marek-czelen/SmartESC_STM32_v2/tools/vcu_esp32.kicad_sch

## KiCad design tools/vcu_esp32.kicad_sch (2026-07-14)

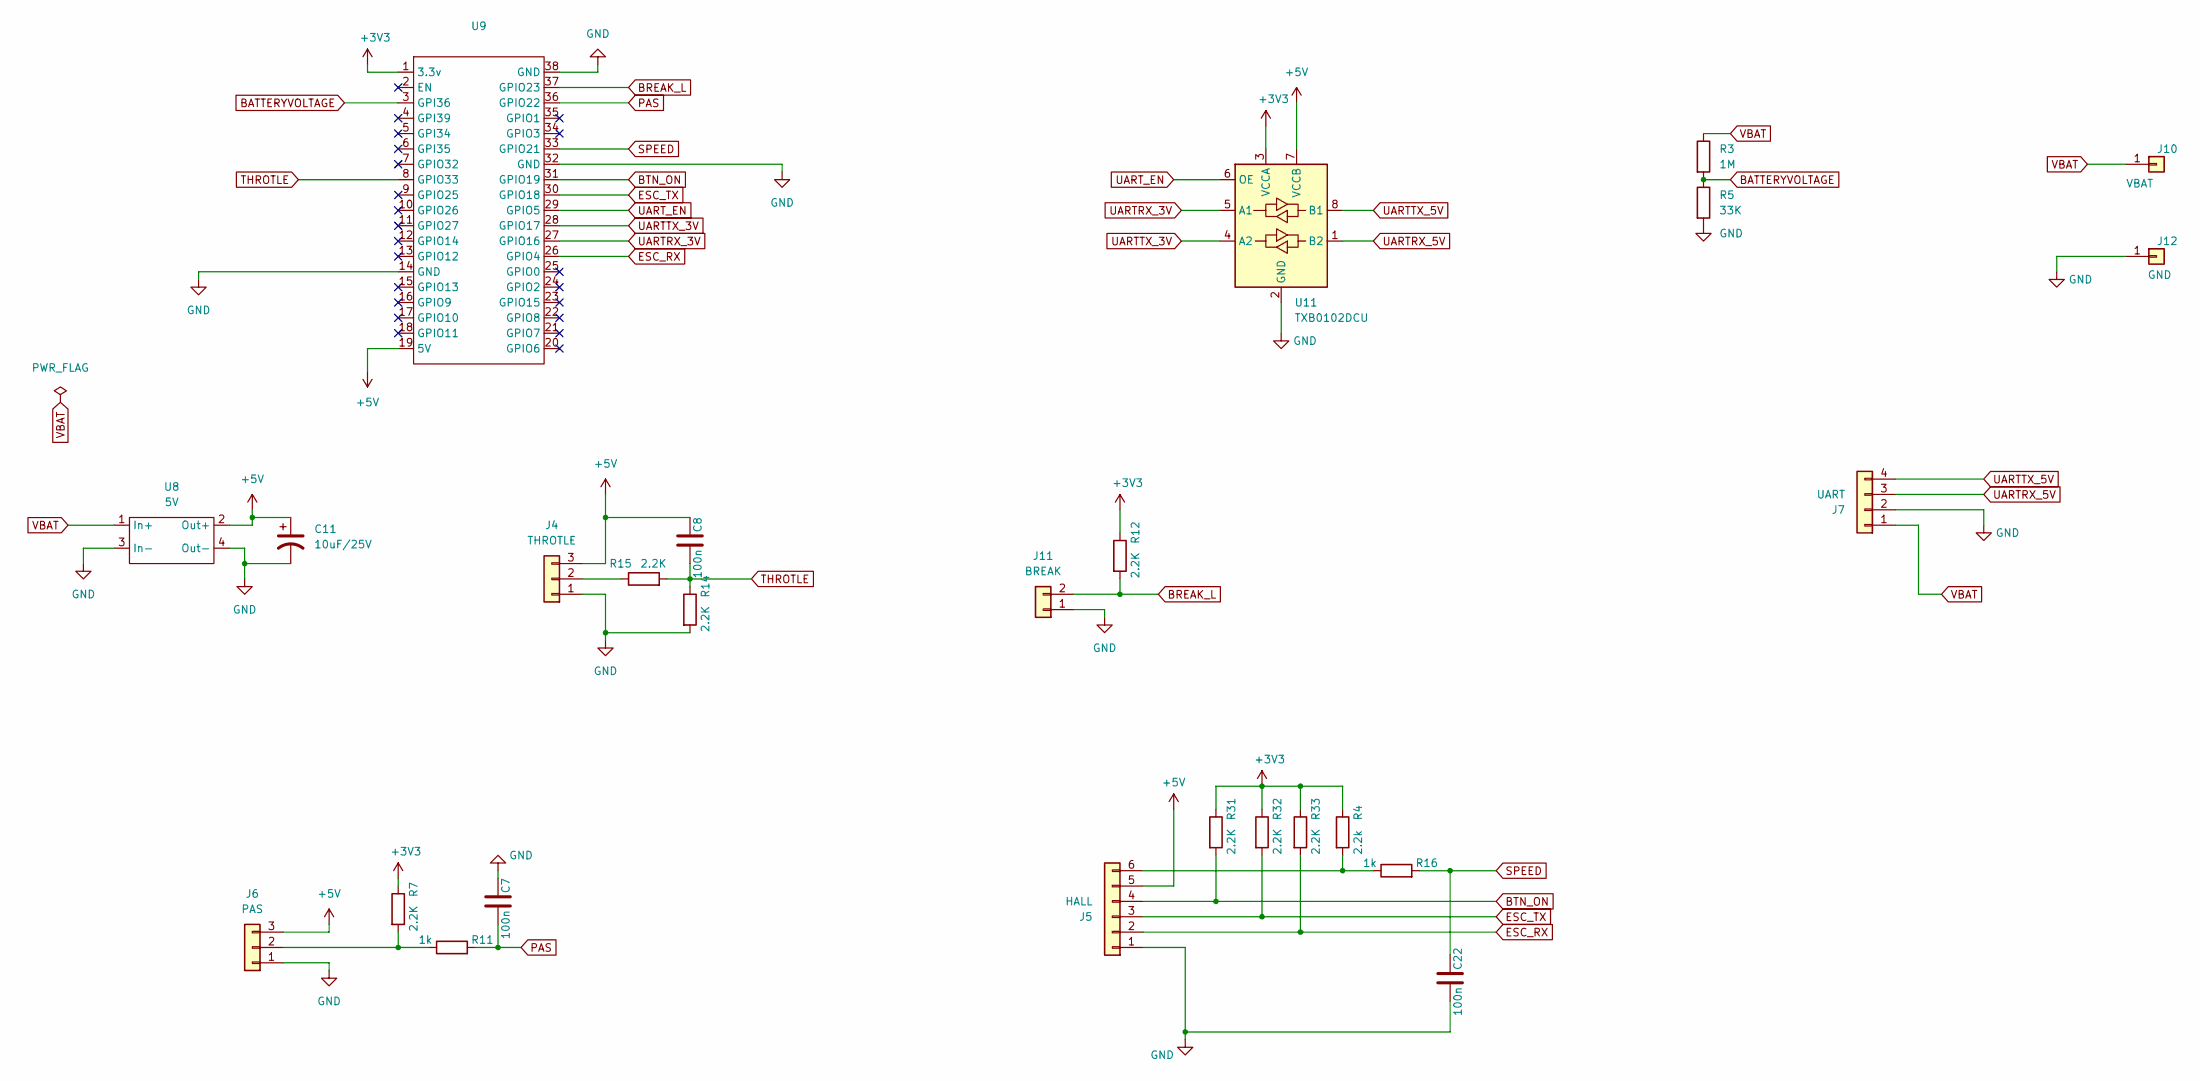
[picture p4: schematic vcu_esp32.kicad_sch]

Parts:
C7, C8, C22: 100n; C_0805_2012Metric
C11: 10uF/25V; CP_Radial_D5.0mm_P2.00mm
J4: THROTLE; PinSocket_1x03_P2.54mm_Vertical
J5: HALL; PinSocket_1x06_P2.54mm_Vertical
J6: PAS; PinSocket_1x03_P2.54mm_Vertical
J7: UART; PinSocket_1x04_P2.54mm_Vertical
J10: VBAT; SolderWire-2.5sqmm_1x01_D2.4mm_OD3.6mm
J11: BREAK; PinSocket_1x02_P2.54mm_Vertical
J12: GND; SolderWire-2.5sqmm_1x01_D2.4mm_OD3.6mm
R3: 1M; R_0805_2012Metric
R4: 2.2k; R_0805_2012Metric
R5: 33K; R_0805_2012Metric
R7, R12, R14, R15, R31, R32, R33: 2.2K; R_0805_2012Metric
R11, R16: 1k; R_0805_2012Metric
U8: 5V; dcdc 5..80V-3.3V
U9: Z_ESP32_DevKitC_38pin_socket
U11: TXB0102DCU; VSSOP-8_2.3x2mm_P0.5mm

Connections:
+3V3: R4.1, R7.1, R12.1, R31.1, R32.1, R33.1, U9.1 (3.3v), U11.3 (VCCA)
+5V: C8.1, C11.1, J4.3, J5.5, J6.3, U8.2 (Out+), U9.19 (5V), U11.7 (VCCB)
BATTERYVOLTAGE: R3.2, R5.1, U9.3 (GPI36)
BREAK_L: J11.2, R12.2, U9.37 (GPIO23)
BTN_ON: J5.4, R31.2, U9.31 (GPIO19)
ESC_RX: J5.2, R33.2, U9.26 (GPIO4)
ESC_TX: J5.3, R32.2, U9.30 (GPIO18)
GND: C7.1, C11.2, C22.2, J4.1, J5.1, J6.1, J7.2, J11.1, J12.1, R5.2, R14.2, U8.3 (In-), U8.4 (Out-), U9.14 (GND), U9.32 (GND), U9.38 (GND), U11.2 (GND)
unnamed: J4.2, R15.1
unnamed: J5.6, R4.2, R16.1
unnamed: J6.2, R7.2, R11.1
PAS: C7.2, R11.2, U9.36 (GPIO22)
SPEED: C22.1, R16.2, U9.33 (GPIO21)
THROTLE: C8.2, R14.1, R15.2, U9.8 (GPIO33)
UARTRX_3V: U9.27 (GPIO16), U11.5 (A1)
UARTRX_5V: J7.3, U11.1 (B2)
UARTTX_3V: U9.28 (GPIO17), U11.4 (A2)
UARTTX_5V: J7.4, U11.8 (B1)
UART_EN: U9.29 (GPIO5), U11.6 (OE)
VBAT: J7.1, J10.1, R3.1, U8.1 (In+)
