marek-czelen/SmartESC_STM32_v2/common_files/MotorControl/MCSDK/MCLib/Any/Inc/enc_align_ctrl.h

/**
  ******************************************************************************
  * @file    enc_align_ctrl.h
  * @author  Motor Control SDK Team, ST Microelectronics
  * @brief   This file contains all definitions and functions prototypes for the
  *          Encoder Alignment Control component of the Motor Control SDK.
  ******************************************************************************
  * @attention
  *
  * <h2><center>&copy; Copyright (c) 2019 STMicroelectronics.
  * All rights reserved.</center></h2>
  *
  * This software component is licensed by ST under Ultimate Liberty license
  * SLA0044, the "License"; You may not use this file except in compliance with
  * the License. You may obtain a copy of the License at:
  *                             www.st.com/SLA0044
  *
  ******************************************************************************
  * @ingroup EncAlignCtrl
  */


/* Define to prevent recursive inclusion -------------------------------------*/
#ifndef __ENCALIGNCTRLCLASS_H
#define __ENCALIGNCTRLCLASS_H

#ifdef __cplusplus
extern "C" {
#endif /* __cplusplus */

/* Includes ------------------------------------------------------------------*/
#include "mc_type.h"
#include "speed_torq_ctrl.h"
#include "virtual_speed_sensor.h"
#include "encoder_speed_pos_fdbk.h"

/** @addtogroup MCSDK
  * @{
  */

/** @addtogroup EncAlignCtrl
  * @{
  */

/**
  * @brief  This structure is used to handle an instance of  EncAlignCtrl component
  */

typedef struct
{
  SpeednTorqCtrl_Handle_t * pSTC;       /*!< Speed and torque controller object used by  EAC.*/
  VirtualSpeedSensor_Handle_t * pVSS;   /*!< Virtual speed sensor object used by EAC.*/
  ENCODER_Handle_t * pENC;              /*!< Encoder object used by EAC.*/
  uint16_t hRemainingTicks;             /*!< Number of clock events remaining to complete
                                             the alignment.*/
  bool EncAligned;   /*!< This flag is true if the encoder has been
                               aligned at least one time, false if hasn't been
                                never aligned.*/
  bool EncRestart;   /*!< This flag is used to force a restart of the
                                motorafter the encoder alignment. It is true
                                if a restart is programmed else false*/
  uint16_t hEACFrequencyHz; /*!< Frequency expressed in Hz at which the user
                                 clocks the EAC calling EAC_Exec method */
  int16_t hFinalTorque;     /*!< Motor torque reference imposed by STC at the
                                 end of programmed alignment. This value
                                 represents actually the Iq current expressed in
                                 digit.*/
  int16_t hElAngle;        /*!< Electrical angle of programmed alignment
                                 expressed in s16degrees.*/
  uint16_t hDurationms;     /*!< Duration of the programmed alignment expressed
                                 in milliseconds.*/
  uint8_t bElToMecRatio;    /*!< Coefficient used to transform electrical to
                                 mechanical quantities and viceversa. It usually
                                 coincides with motor pole pairs number*/
} EncAlign_Handle_t;


/* Exported functions ------------------------------------------------------- */

/*  Function used to initialize an instance of the EncAlignCtrl component */
void EAC_Init( EncAlign_Handle_t * pHandle, SpeednTorqCtrl_Handle_t * pSTC, VirtualSpeedSensor_Handle_t * pVSS,
               ENCODER_Handle_t * pENC );

/* Function used to start the encoder alignment procedure.*/
void EAC_StartAlignment( EncAlign_Handle_t * pHandle );

/* Function used to clocks the encoder alignment controller*/
bool EAC_Exec( EncAlign_Handle_t * pHandle );

/* It returns true if the encoder has been aligned at least one time*/
bool EAC_IsAligned( EncAlign_Handle_t * pHandle );

/* It sets a restart after an encoder alignment*/
void EAC_SetRestartState( EncAlign_Handle_t * pHandle, bool restart );

/* Returns true if a restart after an encoder alignment has been requested*/
bool EAC_GetRestartState( EncAlign_Handle_t * pHandle );

/**
  * @}
  */

/**
  * @}
  */
#ifdef __cplusplus
}
#endif /* __cpluplus */

#endif /* __ENCALIGNCTRLCLASS_H */

/******************* (C) COPYRIGHT 2019 STMicroelectronics *****END OF FILE****/
