marek-czelen/SmartESC_STM32_v2/common_files/MotorControl/MCSDK/MCLib/Any/Inc/pqd_motor_power_measurement.h

/**
  ******************************************************************************
  * @file    pqd_motor_power_measurement.h
  * @author  Motor Control SDK Team, ST Microelectronics
  * @brief   This file contains all definitions and functions prototypes for the
  *          pqd_motor_power_measurement component of the Motor Control SDK.
  ******************************************************************************
  * @attention
  *
  * <h2><center>&copy; Copyright (c) 2019 STMicroelectronics.
  * All rights reserved.</center></h2>
  *
  * This software component is licensed by ST under Ultimate Liberty license
  * SLA0044, the "License"; You may not use this file except in compliance with
  * the License. You may obtain a copy of the License at:
  *                             www.st.com/SLA0044
  *
  ******************************************************************************
  * @ingroup motorpowermeasurement
  */

/* Define to prevent recursive inclusion -------------------------------------*/
#ifndef __PQD_MOTORPOWERMEASUREMENT_H
#define __PQD_MOTORPOWERMEASUREMENT_H

#ifdef __cplusplus
extern "C" {
#endif /* __cplusplus */

/* Includes ------------------------------------------------------------------*/
#include "motor_power_measurement.h"
#include "bus_voltage_sensor.h"


/** @addtogroup MCSDK
  * @{
  */

/** @addtogroup motorpowermeasurement
  * @{
  */

/** @addtogroup pqd_motorpowermeasurement
  * @{
  */

typedef struct
{
  MotorPowMeas_Handle_t _super;

  int32_t wConvFact; /* It is the conversion factor used to convert the
                         variables expressed in digit into variables expressed
                         in physical measurement unit. It is used to convert the
                         power in watts. It must be equal to
                         (1000 * 3 * Vddï¿½)/(sqrt(3) * Rshunt * Aop) */

  pFOCVars_t pFOCVars;    /*!< Pointer to FOC vars used by MPM.*/
  BusVoltageSensor_Handle_t * pVBS;              /*!< Bus voltage sensor object used by MPM.*/
  uint16_t meas_count;
} PQD_MotorPowMeas_Handle_t;



/**
  * @brief Implementation of derived class init method. It should be called before each motor restart.
  * @param pHandle related component instance.
  * @retval none.
  */
void PQD_Clear( PQD_MotorPowMeas_Handle_t * pHandle );

/**
  * @brief Implementation of derived class CalcElMotorPower.
  * @param pHandle related component instance.
  * @retval int16_t The measured motor power expressed in watt.
  */
void PQD_CalcElMotorPower( PQD_MotorPowMeas_Handle_t * pHandle );


/**
  * @}
  */

/**
  * @}
  */

/** @} */
#ifdef __cplusplus
}
#endif /* __cpluplus */

#endif /* __CCC_H */

/************************ (C) COPYRIGHT 2019 STMicroelectronics *****END OF FILE****/
