marek-czelen/SmartESC_STM32_v2/common_files/MotorControl/MCSDK/MCLib/Any/Src/r_divider_bus_voltage_sensor.c

/**
  ******************************************************************************
  * @file    r_divider_bus_voltage_sensor.c
  * @author  Motor Control SDK Team, ST Microelectronics
  * @brief   This file provides firmware functions that implement the  features
  *          of the Resistor Divider Bus Voltage Sensor component of the Motor
  *          Control SDK:
  *
  ******************************************************************************
  * @attention
  *
  * <h2><center>&copy; Copyright (c) 2019 STMicroelectronics.
  * All rights reserved.</center></h2>
  *
  * This software component is licensed by ST under Ultimate Liberty license
  * SLA0044, the "License"; You may not use this file except in compliance with
  * the License. You may obtain a copy of the License at:
  *                             www.st.com/SLA0044
  *
  ******************************************************************************
  */

/* Includes ------------------------------------------------------------------*/
#include "r_divider_bus_voltage_sensor.h"
#include "regular_conversion_manager.h"


/** @addtogroup MCSDK
  * @{
  */

/** @addtogroup BusVoltageSensor
  * @{
  */

/** @defgroup RDividerBusVoltageSensor Resistor Divider Bus Voltage Sensor
  * @brief Resistor Divider Bus Voltage Sensor implementation
  *
  * @todo Document the Resistor Divider Bus Voltage Sensor "module".
  *
  * @{
  */

/**
  * @brief  It initializes bus voltage conversion (ADC, ADC channel, conversion time. 
    It must be called only after PWMC_Init.
  * @param  pHandle related RDivider_Handle_t
  * @retval none
  */
__weak void RVBS_Init( RDivider_Handle_t * pHandle )
{
  /* Need to be register with RegularConvManager */
  pHandle->convHandle = RCM_RegisterRegConv(&pHandle->VbusRegConv);
  /* Check */
  RVBS_Clear( pHandle );
}


/**
  * @brief  It clears bus voltage FW variable containing average bus voltage
  *         value
  * @param  pHandle related RDivider_Handle_t
  * @retval none
  */
__weak void RVBS_Clear( RDivider_Handle_t * pHandle )
{
  uint16_t aux;
  uint16_t index;

  aux = ( pHandle->OverVoltageThreshold + pHandle->UnderVoltageThreshold ) / 2u;
  for ( index = 0u; index < pHandle->LowPassFilterBW; index++ )
  {
    pHandle->aBuffer[index] = aux;
  }
  pHandle->_Super.LatestConv = aux;
  pHandle->_Super.AvBusVoltage_d = aux;
  pHandle->index = 0;
}

static uint16_t RVBS_ConvertVbusFiltrered( RDivider_Handle_t * pHandle )
{
  uint16_t hAux;
  uint8_t vindex;
  uint16_t max = 0, min = 0;
  uint32_t tot = 0u;

  for ( vindex = 0; vindex < pHandle->LowPassFilterBW; )
  {
    hAux = RCM_ExecRegularConv(pHandle->convHandle);

    if ( hAux != 0xFFFFu )
    {
      if ( vindex == 0 )
      {
        min = hAux;
        max = hAux;
      }
      else
      {
        if ( hAux < min )
        {
          min = hAux;
        }
        if ( hAux > max )
        {
          max = hAux;
        }
      }
      vindex++;

      tot += hAux;
    }
  }

  tot -= max;
  tot -= min;
  return ( uint16_t )( tot / ( pHandle->LowPassFilterBW - 2u ) );
}

/**
  * @brief  It actually performes the Vbus ADC conversion and updates average
  *         value
  * @param  pHandle related RDivider_Handle_t
  * @retval uint16_t Fault code error
  */
__weak uint16_t RVBS_CalcAvVbusFilt( RDivider_Handle_t * pHandle )
{
  uint32_t wtemp;
  uint16_t hAux;
  uint8_t i;

  hAux = RVBS_ConvertVbusFiltrered( pHandle );

  if ( hAux != 0xFFFF )
  {
    pHandle->aBuffer[pHandle->index] = hAux;
    wtemp = 0;
    for ( i = 0; i < pHandle->LowPassFilterBW; i++ )
    {
      wtemp += pHandle->aBuffer[i];
    }
    wtemp /= pHandle->LowPassFilterBW;
    pHandle->_Super.AvBusVoltage_d = ( uint16_t )wtemp;
    pHandle->_Super.LatestConv = hAux;

    if ( pHandle->index < pHandle->LowPassFilterBW - 1 )
    {
      pHandle->index++;
    }
    else
    {
      pHandle->index = 0;
    }
  }

  pHandle->_Super.FaultState = RVBS_CheckFaultState( pHandle );

  return ( pHandle->_Super.FaultState );
}

/**
  * @brief  It actually performes the Vbus ADC conversion and updates average
  *         value
  * @param  pHandle related RDivider_Handle_t
  * @retval uint16_t Fault code error
  */
__weak uint16_t RVBS_CalcAvVbus( RDivider_Handle_t * pHandle )
{
  uint32_t wtemp;
  uint16_t hAux;
  uint8_t i;

  hAux = RCM_ExecRegularConv(pHandle->convHandle);

  if ( hAux != 0xFFFF )
  {
    pHandle->aBuffer[pHandle->index] = hAux;
    wtemp = 0;
    for ( i = 0; i < pHandle->LowPassFilterBW; i++ )
    {
      wtemp += pHandle->aBuffer[i];
    }
    wtemp /= pHandle->LowPassFilterBW;
    pHandle->_Super.AvBusVoltage_d = ( uint16_t )wtemp;
    pHandle->_Super.LatestConv = hAux;

    if ( pHandle->index < pHandle->LowPassFilterBW - 1 )
    {
      pHandle->index++;
    }
    else
    {
      pHandle->index = 0;
    }
  }

  pHandle->_Super.FaultState = RVBS_CheckFaultState( pHandle );

  return ( pHandle->_Super.FaultState );
}

/**
  * @brief  It returns MC_OVER_VOLT, MC_UNDER_VOLT or MC_NO_ERROR depending on
  *         bus voltage and protection threshold values
  * @param  pHandle related RDivider_Handle_t
  * @retval uint16_t Fault code error
  */
__weak uint16_t RVBS_CheckFaultState( RDivider_Handle_t * pHandle )
{
  uint16_t fault;

  if ( (pHandle->OverVoltageThreshold > 0) && (pHandle->_Super.AvBusVoltage_d > pHandle->OverVoltageThreshold))
  {
		fault = MC_OVER_VOLT;
  }
  else if ( (pHandle->UnderVoltageThreshold > 0) && (pHandle->_Super.AvBusVoltage_d < pHandle->UnderVoltageThreshold))
  {

    fault = MC_UNDER_VOLT;
  }
  else
  {
    fault = MC_NO_ERROR;
  }
  return fault;
}


/**
  * @}
  */

/**
  * @}
  */

/** @} */

/************************ (C) COPYRIGHT 2019 STMicroelectronics *****END OF FILE****/
