marek-czelen/SmartESC_STM32_v2/common_files/inc/mcconf_default.h

/*
	Copyright 2016 - 2019 Benjamin Vedder	benjamin@vedder.se

	This file is part of the VESC firmware.

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
    You should have received a copy of the GNU General Public License
    along with this program.  If not, see <http://www.gnu.org/licenses/>.
    */

#ifndef MCCONF_DEFAULT_H_
#define MCCONF_DEFAULT_H_

// Default settings
#ifndef MCCONF_DEFAULT_MOTOR_TYPE
#define MCCONF_DEFAULT_MOTOR_TYPE		MOTOR_TYPE_FOC
#endif
#ifndef MCCONF_PWM_MODE
#define MCCONF_PWM_MODE					PWM_MODE_SYNCHRONOUS // Default PWM mode
#endif
#ifndef MCCONF_SENSOR_MODE
#define MCCONF_SENSOR_MODE				SENSOR_MODE_SENSORED // Sensor mode
#endif
#ifndef MCCONF_COMM_MODE
#define MCCONF_COMM_MODE				COMM_MODE_INTEGRATE	// The commutation mode to use
#endif

// Limits
#ifndef MCCONF_L_CURRENT_MAX
#define MCCONF_L_CURRENT_MAX			30.0	// Current limit in Amperes (Upper)
#endif
#ifndef MCCONF_L_CURRENT_MIN
#define MCCONF_L_CURRENT_MIN			-30.0	// Current limit in Amperes (Lower)
#endif
#ifndef MCCONF_L_IN_CURRENT_MAX
#define MCCONF_L_IN_CURRENT_MAX			20.0	// Input current limit in Amperes (Upper)
#endif
#ifndef MCCONF_L_IN_CURRENT_MIN
#define MCCONF_L_IN_CURRENT_MIN			-20.0	// Input current limit in Amperes (Lower)
#endif
#ifndef MCCONF_L_MAX_ABS_CURRENT
#define MCCONF_L_MAX_ABS_CURRENT		60.0	// The maximum absolute current above which a fault is generated
#endif
#ifndef MCCONF_L_MIN_VOLTAGE
#define MCCONF_L_MIN_VOLTAGE			8.0		// Minimum input voltage
#endif
#ifndef MCCONF_L_MAX_VOLTAGE
#define MCCONF_L_MAX_VOLTAGE			56.0	// Maximum input voltage
#endif
#ifndef MCCONF_L_BATTERY_CUT_START
#define MCCONF_L_BATTERY_CUT_START		34.0	// Start limiting the positive current at this voltage
#endif
#ifndef MCCONF_L_BATTERY_CUT_END
#define MCCONF_L_BATTERY_CUT_END		30.0		// Limit the positive current completely at this voltage
#endif
#ifndef MCCONF_L_RPM_MAX
#define MCCONF_L_RPM_MAX				60000.0	// The motor speed limit (Upper)
#endif
#ifndef MCCONF_L_RPM_MIN
#define MCCONF_L_RPM_MIN				-60000.0	// The motor speed limit (Lower)
#endif
#ifndef MCCONF_L_RPM_START
#define MCCONF_L_RPM_START				1.0		// Fraction of full speed where RPM current limiting starts
#endif
#ifndef MCCONF_L_SLOW_ABS_OVERCURRENT
#define MCCONF_L_SLOW_ABS_OVERCURRENT	true	// Use the filtered (and hence slower) current for the overcurrent fault detection
#endif
#ifndef MCCONF_L_MIN_DUTY
#define MCCONF_L_MIN_DUTY				0.00	// Minimum duty cycle
#endif
#ifndef MCCONF_L_MAX_DUTY
#define MCCONF_L_MAX_DUTY				0.99	// Maximum duty cycle
#endif
#ifndef MCCONF_L_CURR_MAX_RPM_FBRAKE
#define MCCONF_L_CURR_MAX_RPM_FBRAKE	300		// Maximum electrical RPM to use full brake at
#endif
#ifndef MCCONF_L_CURR_MAX_RPM_FBRAKE_CC
#define MCCONF_L_CURR_MAX_RPM_FBRAKE_CC	1500	// Maximum electrical RPM to use full brake at with current control
#endif
#ifndef MCCONF_L_LIM_TEMP_FET_START
#define MCCONF_L_LIM_TEMP_FET_START		65.0	// MOSFET temperature where current limiting should begin
#endif
#ifndef MCCONF_L_LIM_TEMP_FET_END
#define MCCONF_L_LIM_TEMP_FET_END		75.0	// MOSFET temperature where everything should be shut off
#endif
#ifndef MCCONF_L_LIM_TEMP_MOTOR_START
#define MCCONF_L_LIM_TEMP_MOTOR_START	0.0	// MOTOR temperature where current limiting should begin
#endif
#ifndef MCCONF_L_LIM_TEMP_MOTOR_END
#define MCCONF_L_LIM_TEMP_MOTOR_END		75.0	// MOTOR temperature where everything should be shut off
#endif
#ifndef MCCONF_L_LIM_TEMP_ACCEL_DEC
#define MCCONF_L_LIM_TEMP_ACCEL_DEC		0.15	// Decrease temperature limits this much during acceleration
#endif
#ifndef MCCONF_L_WATT_MAX
#define MCCONF_L_WATT_MAX				1500000.0	// Maximum wattage output
#endif
#ifndef MCCONF_L_WATT_MIN
#define MCCONF_L_WATT_MIN				-1500000.0	// Minimum wattage output (braking)
#endif
#ifndef MCCONF_L_CURRENT_MAX_SCALE
#define MCCONF_L_CURRENT_MAX_SCALE		1.0	// Maximum current scale
#endif
#ifndef MCCONF_L_CURRENT_MIN_SCALE
#define MCCONF_L_CURRENT_MIN_SCALE		1.0	// Minimum current scale
#endif
#ifndef MCCONF_L_DUTY_START
#define MCCONF_L_DUTY_START				1.0 // Start limiting current at this duty cycle
#endif

// Speed PID parameters
#ifndef MCCONF_S_PID_KP
#define MCCONF_S_PID_KP					2	// Proportional gain
#endif
#ifndef MCCONF_S_PID_KI
#define MCCONF_S_PID_KI					5	// Integral gain
#endif
#ifndef MCCONF_S_PID_KD
#define MCCONF_S_PID_KD					0.0	// Derivative gain
#endif
#ifndef MCCONF_S_PID_KD_FILTER
#define MCCONF_S_PID_KD_FILTER			0.2	// Derivative filter
#endif
#ifndef MCCONF_S_PID_MIN_RPM
#define MCCONF_S_PID_MIN_RPM			0.0	// Minimum allowed RPM
#endif
#ifndef MCCONF_S_PID_ALLOW_BRAKING
#define MCCONF_S_PID_ALLOW_BRAKING		false	// Allow braking in speed control mode
#endif
#ifndef MCCONF_S_PID_RAMP_ERPMS_S
#define MCCONF_S_PID_RAMP_ERPMS_S		0.0	// Default Speed Input Ramp
#endif

// Position PID parameters
#ifndef MCCONF_P_PID_KP
#define MCCONF_P_PID_KP					0.03	// Proportional gain
#endif
#ifndef MCCONF_P_PID_KI
#define MCCONF_P_PID_KI					0.0		// Integral gain
#endif
#ifndef MCCONF_P_PID_KD
#define MCCONF_P_PID_KD					0.0004	// Derivative gain
#endif
#ifndef MCCONF_P_PID_KD_FILTER
#define MCCONF_P_PID_KD_FILTER			0.2		// Derivative filter
#endif
#ifndef MCCONF_P_PID_ANG_DIV
#define MCCONF_P_PID_ANG_DIV			1.0		// Divide angle by this value
#endif

// Current control parameters
#ifndef MCCONF_CC_GAIN
#define MCCONF_CC_GAIN					0.0046	// Current controller error gain
#endif
#ifndef MCCONF_CC_MIN_CURRENT
#define MCCONF_CC_MIN_CURRENT			0.05	// Minimum allowed current
#endif
#ifndef MCCONF_CC_STARTUP_BOOST_DUTY
#define MCCONF_CC_STARTUP_BOOST_DUTY	0.01	// The lowest duty cycle to use in current control mode (has to be > MCPWM_MIN_DUTY_CYCLE)
#endif
#ifndef MCCONF_CC_RAMP_STEP
#define MCCONF_CC_RAMP_STEP				0.04	// Maximum duty cycle ramping step in CC mode
#endif

// BLDC
#ifndef MCCONF_SL_MIN_RPM
#define MCCONF_SL_MIN_RPM				150		// Auto-commutate below this RPM
#endif
#ifndef MCCONF_SL_MIN_ERPM_CYCLE_INT_LIMIT
#define MCCONF_SL_MIN_ERPM_CYCLE_INT_LIMIT	1100.0	// Minimum RPM to calculate the BEMF coupling from
#endif
#ifndef MCCONF_SL_CYCLE_INT_LIMIT
#define MCCONF_SL_CYCLE_INT_LIMIT		62.0	// Flux integrator limit 0 ERPM
#endif
#ifndef MCCONF_SL_BEMF_COUPLING_K
#define MCCONF_SL_BEMF_COUPLING_K		600.0	// Input voltage to bemf coupling constant
#endif
#ifndef MCCONF_SL_PHASE_ADVANCE_AT_BR
#define MCCONF_SL_PHASE_ADVANCE_AT_BR	0.8		// Flux integrator limit percentage at MCPWM_CYCLE_INT_START_RPM_BR ERPM
#endif
#ifndef MCCONF_SL_CYCLE_INT_BR
#define MCCONF_SL_CYCLE_INT_BR			80000.0	// RPM border between the START and LOW interval
#endif
#ifndef MCCONF_SL_MAX_FB_CURR_DIR_CHANGE
#define MCCONF_SL_MAX_FB_CURR_DIR_CHANGE	10.0	// Maximum current during full brake during which a direction change is allowed
#endif

// BLDC hall sensor table
#ifndef MCCONF_HALL_TAB_0
#define MCCONF_HALL_TAB_0				-1
#endif
#ifndef MCCONF_HALL_TAB_1
#define MCCONF_HALL_TAB_1				1
#endif
#ifndef MCCONF_HALL_TAB_2
#define MCCONF_HALL_TAB_2				3
#endif
#ifndef MCCONF_HALL_TAB_3
#define MCCONF_HALL_TAB_3				2
#endif
#ifndef MCCONF_HALL_TAB_4
#define MCCONF_HALL_TAB_4				5
#endif
#ifndef MCCONF_HALL_TAB_5
#define MCCONF_HALL_TAB_5				6
#endif
#ifndef MCCONF_HALL_TAB_6
#define MCCONF_HALL_TAB_6				4
#endif
#ifndef MCCONF_HALL_TAB_7
#define MCCONF_HALL_TAB_7				-1
#endif
#ifndef MCCONF_HALL_ERPM
#define MCCONF_HALL_ERPM				2000.0	// ERPM above which sensorless commutation is used in hybrid mode
#endif

// FOC
#ifndef MCCONF_FOC_CURRENT_KP
#define MCCONF_FOC_CURRENT_KP			0.09
#endif
#ifndef MCCONF_FOC_CURRENT_KI
#define MCCONF_FOC_CURRENT_KI			110.0
#endif
#ifndef MCCONF_FOC_F_SW
#define MCCONF_FOC_F_SW					16000.0
#endif
#ifndef MCCONF_FOC_DT_US
#define MCCONF_FOC_DT_US				0.12 // Microseconds for dead time compensation
#endif
#ifndef MCCONF_FOC_ENCODER_INVERTED
#define MCCONF_FOC_ENCODER_INVERTED		false
#endif
#ifndef MCCONF_FOC_ENCODER_OFFSET
#define MCCONF_FOC_ENCODER_OFFSET		90.0
#endif
#ifndef MCCONF_FOC_ENCODER_RATIO
#define MCCONF_FOC_ENCODER_RATIO		7.0
#endif
#ifndef MCCONF_FOC_SENSOR_MODE
#define MCCONF_FOC_SENSOR_MODE			FOC_SENSOR_MODE_SENSORLESS
#endif
#ifndef MCCONF_FOC_PLL_KP
#define MCCONF_FOC_PLL_KP				2000.0
#endif
#ifndef MCCONF_FOC_PLL_KI
#define MCCONF_FOC_PLL_KI				30000.0
#endif
#ifndef MCCONF_FOC_MOTOR_L
#define MCCONF_FOC_MOTOR_L				0.0001
#endif
#ifndef MCCONF_FOC_MOTOR_R
#define MCCONF_FOC_MOTOR_R				0.1
#endif
#ifndef MCCONF_FOC_MOTOR_FLUX_LINKAGE
#define MCCONF_FOC_MOTOR_FLUX_LINKAGE	0.012
#endif
#ifndef MCCONF_FOC_MOTOR_LD_LQ_DIFF
#define MCCONF_FOC_MOTOR_LD_LQ_DIFF		0.0
#endif
#ifndef MCCONF_FOC_OBSERVER_GAIN
#define MCCONF_FOC_OBSERVER_GAIN		9e7		// Can be something like 600 / L
#endif
#ifndef MCCONF_FOC_OBSERVER_GAIN_SLOW
#define MCCONF_FOC_OBSERVER_GAIN_SLOW	0.05	// Observer gain scale at minimum duty cycle
#endif
#ifndef MCCONF_FOC_DUTY_DOWNRAMP_KP
#define MCCONF_FOC_DUTY_DOWNRAMP_KP		10.0	// PI controller for duty control when decreasing the duty
#endif
#ifndef MCCONF_FOC_DUTY_DOWNRAMP_KI
#define MCCONF_FOC_DUTY_DOWNRAMP_KI		200.0	// PI controller for duty control when decreasing the duty
#endif
#ifndef MCCONF_FOC_OPENLOOP_RPM
#define MCCONF_FOC_OPENLOOP_RPM			1500.0	// Openloop RPM (sensorless low speed or when finding index pulse)
#endif
#ifndef MCCONF_FOC_OPENLOOP_RPM_LOW
#define MCCONF_FOC_OPENLOOP_RPM_LOW		0.0		// Fraction of OPENLOOP_RPM at minimum motor current
#endif
#ifndef MCCONF_FOC_D_GAIN_SCALE_START
#define MCCONF_FOC_D_GAIN_SCALE_START	0.9		// Start reducing D axis current controller gain at this modulation
#endif
#ifndef MCCONF_FOC_D_GAIN_SCALE_MAX_MOD
#define MCCONF_FOC_D_GAIN_SCALE_MAX_MOD	0.2		// D axis currnet controller gain at maximum modulation
#endif
#ifndef MCCONF_FOC_SL_OPENLOOP_HYST
#define MCCONF_FOC_SL_OPENLOOP_HYST		0.1		// Time below min RPM to activate openloop (s)
#endif
#ifndef MCCONF_FOC_SL_OPENLOOP_TIME
#define MCCONF_FOC_SL_OPENLOOP_TIME		0.05	// Time to remain in openloop after ramping (s)
#endif
#ifndef MCCONF_FOC_SL_OPENLOOP_T_LOCK
#define MCCONF_FOC_SL_OPENLOOP_T_LOCK	0.0		// Time to lock motor in beginning of open loop sequence
#endif
#ifndef MCCONF_FOC_SL_OPENLOOP_T_RAMP
#define MCCONF_FOC_SL_OPENLOOP_T_RAMP	0.1		// Time to ramp up motor to openloop speed
#endif
#ifndef MCCONF_FOC_HALL_TAB_0
#define MCCONF_FOC_HALL_TAB_0			255
#endif
#ifndef MCCONF_FOC_HALL_TAB_1
#define MCCONF_FOC_HALL_TAB_1			20
#endif
#ifndef MCCONF_FOC_HALL_TAB_2
#define MCCONF_FOC_HALL_TAB_2			104
#endif
#ifndef MCCONF_FOC_HALL_TAB_3
#define MCCONF_FOC_HALL_TAB_3			60
#endif
#ifndef MCCONF_FOC_HALL_TAB_4
#define MCCONF_FOC_HALL_TAB_4			188
#endif
#ifndef MCCONF_FOC_HALL_TAB_5
#define MCCONF_FOC_HALL_TAB_5			232
#endif
#ifndef MCCONF_FOC_HALL_TAB_6
#define MCCONF_FOC_HALL_TAB_6			149
#endif
#ifndef MCCONF_FOC_HALL_TAB_7
#define MCCONF_FOC_HALL_TAB_7			255
#endif
#ifndef MCCONF_FOC_HALL_INTERP_ERPM
#define MCCONF_FOC_HALL_INTERP_ERPM		50		// Do not interpolate hall sensors below this ERPM
#endif
#ifndef MCCONF_FOC_SL_ERPM
#define MCCONF_FOC_SL_ERPM				2500.0	// ERPM above which only the observer is used
#endif
#ifndef MCCONF_FOC_SAMPLE_V0_V7
#define MCCONF_FOC_SAMPLE_V0_V7			false	// Run control loop in both v0 and v7 (requires phase shunts)
#endif
#ifndef MCCONF_FOC_SAMPLE_HIGH_CURRENT
#define MCCONF_FOC_SAMPLE_HIGH_CURRENT	false	// High current sampling mode (requires three shunts)
#endif
#ifndef MCCONF_FOC_SAT_COMP
#define MCCONF_FOC_SAT_COMP				0.0		// Stator saturation compensation
#endif
#ifndef MCCONF_FOC_TEMP_COMP
#define MCCONF_FOC_TEMP_COMP			false	// Motor temperature compensation
#endif
#ifndef MCCONF_FOC_TEMP_COMP_BASE_TEMP
#define MCCONF_FOC_TEMP_COMP_BASE_TEMP	25.0	// Motor temperature compensation base temperature
#endif
#ifndef MCCONF_FOC_CURRENT_FILTER_CONST
#define MCCONF_FOC_CURRENT_FILTER_CONST	0.0		// Filter constant for the filtered currents
#endif
#ifndef MCCONF_FOC_CC_DECOUPLING
#define MCCONF_FOC_CC_DECOUPLING		FOC_CC_DECOUPLING_BEMF // Current controller decoupling
#endif
#ifndef MCCONF_FOC_OBSERVER_TYPE
#define MCCONF_FOC_OBSERVER_TYPE		FOC_OBSERVER_ORTEGA_ORIGINAL // Position observer type for FOC
#endif
#ifndef MCCONF_FOC_HFI_VOLTAGE_START
#define MCCONF_FOC_HFI_VOLTAGE_START	20 // HFI voltage at start when resolving ambiguity
#endif
#ifndef MCCONF_FOC_HFI_VOLTAGE_RUN
#define MCCONF_FOC_HFI_VOLTAGE_RUN		4 // HFI voltage during tracking
#endif
#ifndef MCCONF_FOC_HFI_VOLTAGE_MAX
#define MCCONF_FOC_HFI_VOLTAGE_MAX		10 // HFI voltage during tracking at max current
#endif
#ifndef MCCONF_FOC_SL_ERPM_HFI
#define MCCONF_FOC_SL_ERPM_HFI			2000.0	// ERPM above which only the observer is used
#endif
#ifndef MCCONF_FOC_HFI_START_SAMPLES
#define MCCONF_FOC_HFI_START_SAMPLES	65 // Sample this often at start to resolve ambiguity
#endif
#ifndef MCCONF_FOC_HFI_OBS_OVR_SEC
#define MCCONF_FOC_HFI_OBS_OVR_SEC		0.001 // Continue using observer for this long when entering HFI speed
#endif
#ifndef MCCONF_FOC_HFI_SAMPLES
#define MCCONF_FOC_HFI_SAMPLES			HFI_SAMPLES_16 // Samples per motor revolution for HFI
#endif
#ifndef MCCONF_FOC_MTPA_MODE
#define MCCONF_FOC_MTPA_MODE				MTPA_MODE_OFF // Maximum torque per amp (MTPA) algorithm mode
#endif
#ifndef MCCONF_FOC_FW_CURRENT_MAX
#define MCCONF_FOC_FW_CURRENT_MAX		0.0 // Maximum field weakening current
#endif
#ifndef MCCONF_FOC_FW_DUTY_START
#define MCCONF_FOC_FW_DUTY_START		0.95 // Start field weakening at this fraction of max duty cycle
#endif
#ifndef MCCONF_FOC_FW_RAMP_TIME
#define MCCONF_FOC_FW_RAMP_TIME			0.2 // Ramp time for field weakening current
#endif
#ifndef MCCONF_FOC_FW_Q_CURRENT_FACTOR
#define MCCONF_FOC_FW_Q_CURRENT_FACTOR	0.02 // Factor of the FW-current to feed to the Q-axis to slow motor down when setting 0 current
#endif

// GPD
#ifndef MCCONF_GPD_BUFFER_NOTIFY_LEFT
#define MCCONF_GPD_BUFFER_NOTIFY_LEFT	200		// Notify when the buffer space left is less than this
#endif
#ifndef MCCONF_GPD_BUFFER_INTERPOL
#define MCCONF_GPD_BUFFER_INTERPOL		0		// Buffer interpolation
#endif
#ifndef MCCONF_GPD_CURRENT_FILTER_CONST
#define MCCONF_GPD_CURRENT_FILTER_CONST	0.1		// Current filter constant
#endif
#ifndef MCCONF_GPD_CURRENT_KP
#define MCCONF_GPD_CURRENT_KP			0.03
#endif
#ifndef MCCONF_GPD_CURRENT_KI
#define MCCONF_GPD_CURRENT_KI			50.0
#endif

// Misc
#ifndef MCCONF_M_FAULT_STOP_TIME
#define MCCONF_M_FAULT_STOP_TIME		1000	// Ignore commands for this duration in msec when faults occur
#endif
#ifndef MCCONF_M_RAMP_STEP
#define MCCONF_M_RAMP_STEP				0.02	// Duty cycle ramping step (1000 times/sec) at maximum duty cycle
#endif
#ifndef MCCONF_M_CURRENT_BACKOFF_GAIN
#define MCCONF_M_CURRENT_BACKOFF_GAIN	0.5		// The error gain of the current limiting algorithm
#endif
#ifndef MCCONF_M_ENCODER_COUNTS
#define MCCONF_M_ENCODER_COUNTS			8192	// The number of encoder counts
#endif
#ifndef MCCONF_FOC_ENCODER_SIN_GAIN
#define MCCONF_FOC_ENCODER_SIN_GAIN		1.0		// Sine error gain of the sin/cos encoder
#endif
#ifndef MCCONF_FOC_ENCODER_SIN_OFFSET
#define MCCONF_FOC_ENCODER_SIN_OFFSET		1.65	// Sine offset of the sin/cos encoder
#endif
#ifndef MCCONF_FOC_ENCODER_COS_GAIN
#define MCCONF_FOC_ENCODER_COS_GAIN		1.0		// Cosine error gain of the sin/cos encoder
#endif
#ifndef MCCONF_FOC_ENCODER_COS_OFFSET
#define MCCONF_FOC_ENCODER_COS_OFFSET		1.65	// Cosine offset of the sin/cos encoder
#endif
#ifndef MCCONF_FOC_ENCODER_SINCOS_FILTER
#define MCCONF_FOC_ENCODER_SINCOS_FILTER	0.5		// Sin/Cos Encoder signal filter constant
#endif
#ifndef MCCONF_M_SENSOR_PORT_MODE
#define MCCONF_M_SENSOR_PORT_MODE		SENSOR_PORT_MODE_HALL // The mode of the hall_encoder port
#endif
#ifndef MCCONF_M_INVERT_DIRECTION
#define MCCONF_M_INVERT_DIRECTION		false // Invert the motor direction
#endif
#ifndef MCCONF_M_DRV8301_OC_MODE
#define MCCONF_M_DRV8301_OC_MODE		DRV8301_OC_LIMIT // DRV8301 over current protection mode
#endif
#ifndef MCCONF_M_DRV8301_OC_ADJ
#define MCCONF_M_DRV8301_OC_ADJ			16 // DRV8301 over current protection threshold
#endif
#ifndef MCCONF_M_BLDC_F_SW_MIN
#define MCCONF_M_BLDC_F_SW_MIN			3000 // Minimum switching frequency in bldc mode
#endif
#ifndef MCCONF_M_BLDC_F_SW_MAX
#define MCCONF_M_BLDC_F_SW_MAX			35000 // Maximum switching frequency in bldc mode
#endif
#ifndef MCCONF_M_DC_F_SW
#define MCCONF_M_DC_F_SW				25000 // Switching frequency in dc mode
#endif
#ifndef MCCONF_M_NTC_MOTOR_BETA
#define MCCONF_M_NTC_MOTOR_BETA			3380.0 // Beta value for motor termistor
#endif
#ifndef MCCONF_M_OUT_AUX_MODE
#define MCCONF_M_OUT_AUX_MODE			OUT_AUX_MODE_OFF // Auxiliary output mode
#endif
#ifndef MCCONF_M_MOTOR_TEMP_SENS_TYPE
#define MCCONF_M_MOTOR_TEMP_SENS_TYPE	TEMP_SENSOR_NTC_10K_25C // Motor temperature sensor type
#endif
#ifndef MCCONF_M_PTC_MOTOR_COEFF
#define MCCONF_M_PTC_MOTOR_COEFF		0.61 // %/K coefficient for motor PTC sensor
#endif
#ifndef MCCONF_M_HALL_EXTRA_SAMPLES
#define MCCONF_M_HALL_EXTRA_SAMPLES		1 // Extra samples for filtering when reading hall sensors
#endif

// Setup Info
#ifndef MCCONF_SI_MOTOR_POLES
#define MCCONF_SI_MOTOR_POLES			14 // Motor pole count
#endif
#ifndef MCCONF_SI_GEAR_RATIO
#define MCCONF_SI_GEAR_RATIO			1 // Gear ratio
#endif
#ifndef MCCONF_SI_WHEEL_DIAMETER
#define MCCONF_SI_WHEEL_DIAMETER		0.250 // Wheel Diameter
#endif
#ifndef MCCONF_SI_BATTERY_TYPE
#define MCCONF_SI_BATTERY_TYPE			BATTERY_TYPE_LIION_3_0__4_2 // Battery Type
#endif
#ifndef MCCONF_SI_BATTERY_CELLS
#define MCCONF_SI_BATTERY_CELLS			10 // Battery Cells
#endif
#ifndef MCCONF_SI_BATTERY_AH
#define MCCONF_SI_BATTERY_AH			6.0 // Battery amp hours
#endif

// BMS
#ifndef MCCONF_BMS_TYPE
#define MCCONF_BMS_TYPE					BMS_TYPE_VESC
#endif
#ifndef MCCONF_BMS_T_LIMIT_START
#define MCCONF_BMS_T_LIMIT_START		45
#endif
#ifndef MCCONF_BMS_T_LIMIT_END
#define MCCONF_BMS_T_LIMIT_END			65
#endif
#ifndef MCCONF_BMS_SOC_LIMIT_START
#define MCCONF_BMS_SOC_LIMIT_START		0.05
#endif
#ifndef MCCONF_BMS_SOC_LIMIT_END
#define MCCONF_BMS_SOC_LIMIT_END		0
#endif

#endif /* MCCONF_DEFAULT_H_ */
