marek-czelen/SmartESC_STM32_v2/common_files/MotorControl/MCSDK/MCLib/F1xx/Src/r3_2_f1xx_pwm_curr_fdbk.c

/**
  ******************************************************************************
  * @file    R3_2_pwm_curr_fdbk.c
  * @author  Motor Control SDK Team, ST Microelectronics
  * @brief   This file provides firmware functions that implement the features
  *          of the three shunts current sensing topology.
  *           It is specifically designed for STM32F1xx microcontrollers and
  *          implements the successive sampling of current using two ADCs.
  *           + MCU peripheral and handle initialization function
  *           + three shunt current sensing
  *           + space vector modulation function
  *           + ADC sampling function
  *
  ******************************************************************************
  * @attention
  *
  * <h2><center>&copy; Copyright (c) 2019 STMicroelectronics.
  * All rights reserved.</center></h2>
  *
  * This software component is licensed by ST under Ultimate Liberty license
  * SLA0044, the "License"; You may not use this file except in compliance with
  * the License. You may obtain a copy of the License at:
  *                             www.st.com/SLA0044
  *
  ******************************************************************************
  */

/* Includes ------------------------------------------------------------------*/
#include "pwm_curr_fdbk.h"
#include "pwm_common.h"
#include "r3_2_f1xx_pwm_curr_fdbk.h"

#include "mc_type.h"
#include "stdlib.h"

/** @addtogroup MCSDK
  * @{
  */

/** @addtogroup pwm_curr_fdbk
  * @{
  */

/**
 * @defgroup R3_2_pwm_curr_fdbk PWM & Current Feedback
 *
 * @brief STM32F1, 3-Shunt PWM & Current Feedback implementation
 *
 * This component is used in applications based on an STM32F1 HD & MD MCU
 * and using a three shunt resistors current sensing topology.
 *
 * *STM32F103 High Density* refers to STM32F103xC, STM32F103xD and STM32F103xE MCUs.
 *
 * @todo: TODO: complete documentation.
 * @{
 */

/* Private defines -----------------------------------------------------------*/

#define TIMxCCER_MASK_CH123        ((uint16_t)  (LL_TIM_CHANNEL_CH1|LL_TIM_CHANNEL_CH1N|\
                                                 LL_TIM_CHANNEL_CH2|LL_TIM_CHANNEL_CH2N|\
                                                 LL_TIM_CHANNEL_CH3|LL_TIM_CHANNEL_CH3N))

/* Private function prototypes -----------------------------------------------*/
uint16_t R3_2_WriteTIMRegisters( PWMC_Handle_t * pHdl, uint16_t hCCR4Reg );
void R3_2_HFCurrentsPolarizationAB( PWMC_Handle_t * pHdl, ab_t * pStator_Currents );
void R3_2_HFCurrentsPolarizationC( PWMC_Handle_t * pHdl, ab_t * pStator_Currents );
uint16_t R3_2_SetADCSampPointPolarization( PWMC_Handle_t * pHdl) ;

/* Global functions ---------------------------------------------------------*/

/**
 * @brief  It initializes TIM and ADC for current reading and PWM generation
 *         in 3 Shunt configuration using STM32F1xx.
 * @param  pHandle: handler of the current instance of the PWM component
 * @retval none
 */
__weak void R3_2_Init( PWMC_R3_2_Handle_t * pHandle )
{
  TIM_TypeDef * TIMx = pHandle->pParams_str->TIMx;
  ADC_TypeDef * ADCx_1 = pHandle->pParams_str->ADCx_1;
  ADC_TypeDef * ADCx_2 = pHandle->pParams_str->ADCx_2;

  LL_TIM_DisableCounter( TIMx );

  /* BKIN, if enabled */
  if ( (pHandle->pParams_str->EmergencyStop) != DISABLE )
  {
    LL_TIM_ClearFlag_BRK(TIMx);
    LL_TIM_EnableIT_BRK(TIMx);
  }

  /* Prepare timer for synchronization */
  LL_TIM_GenerateEvent_UPDATE(TIMx);
  
  /* Enable PWM channel */
  LL_TIM_CC_EnableChannel( TIMx, TIMxCCER_MASK_CH123 );

  if ( TIMx == TIM1 )
  {
    /* TIM1 Counter Clock stopped when the core is halted */
    LL_DBGMCU_APB2_GRP1_FreezePeriph(LL_DBGMCU_APB2_GRP1_TIM1_STOP);
    pHandle->ADC_ExternalTriggerInjected = LL_ADC_INJ_TRIG_EXT_TIM1_CH4;
  }
#if defined(TIM8)  
  else
  {
    /* TIM8 Counter Clock stopped when the core is halted */
    LL_DBGMCU_APB2_GRP1_FreezePeriph(LL_DBGMCU_APB2_GRP1_TIM8_STOP);
    pHandle->ADC_ExternalTriggerInjected = LL_ADC_INJ_TRIG_EXT_TIM8_CH4;
  }
#endif

  /* ADCs registers configuration ---------------------------------*/
  /* Enable ADCx_1 and ADCx_2 */
  LL_ADC_Enable( ADCx_1 );
  LL_ADC_Enable( ADCx_2 );

  /* ADCx_1 Injected conversions end interrupt enabling */
  LL_ADC_ClearFlag_JEOS(ADCx_1);
  LL_ADC_EnableIT_JEOS( ADCx_1 );

  
  /* Set CC4 as PWM mode 2 (default) to trig on rising edge */
  pHandle->PWM_Mode = LL_TIM_OCMODE_PWM2;

  pHandle->OverCurrentFlag = false;
  pHandle->_Super.DTTest = 0u;

  pHandle->_Super.OverCurrentCyclesCounter = 0;

}

/**
  * @brief  It stores into the component's handle the voltage present on Ia and
  *         Ib current feedback analog channels when no current is flowing into the
  *         motor
  * @param  pHandle handler of the current instance of the PWM component
  */
__weak void R3_2_CurrentReadingPolarization( PWMC_Handle_t * pHdl )
{
  PWMC_R3_2_Handle_t * pHandle = (PWMC_R3_2_Handle_t *) pHdl;
  TIM_TypeDef*  TIMx = pHandle->pParams_str->TIMx;

  pHandle->PhaseAOffset = 0u;
  pHandle->PhaseBOffset = 0u;
  pHandle->PhaseCOffset = 0u;

  pHandle->PolarizationCounter = 0u;

  LL_TIM_CC_DisableChannel(TIMx, TIMxCCER_MASK_CH123);

  /* Offset Polarization for A & B phases */
  /* Change function to be executed in ADCx_ISR */
  pHandle->_Super.pFctGetPhaseCurrents = &R3_2_HFCurrentsPolarizationAB;
  pHandle->_Super.pFctSetADCSampPointSectX = &R3_2_SetADCSampPointPolarization;

  pHandle->PolarizationSector = SECTOR_4;
  /* Required to force first polarization conversion on SECTOR_4*/
  pHandle->_Super.Sector = SECTOR_4;
  
  R3_2_SwitchOnPWM( &pHandle->_Super );

  /* Wait for NB_CONVERSIONS to be executed */
  waitForPolarizationEnd( TIMx,
  		                  &pHandle->_Super.SWerror,
  						  pHandle->pParams_str->RepetitionCounter,
  						  &pHandle->PolarizationCounter );

  R3_2_SwitchOffPWM( &pHandle->_Super );
  /* Offset Polarization for C phase */
  /* Reset PolarizationCounter */
  pHandle->PolarizationCounter = 0u;

  /* Change function to be executed in ADCx_ISR */
  pHandle->_Super.pFctGetPhaseCurrents = &R3_2_HFCurrentsPolarizationC;

  pHandle->PolarizationSector = SECTOR_1;
  /* Required to force first polarization conversion on SECTOR_1*/
  pHandle->_Super.Sector = SECTOR_1;  
  R3_2_SwitchOnPWM( &pHandle->_Super );

  /* Wait for NB_CONVERSIONS to be executed */
  waitForPolarizationEnd( TIMx,
  		                  &pHandle->_Super.SWerror,
  						  pHandle->pParams_str->RepetitionCounter,
  						  &pHandle->PolarizationCounter );

  R3_2_SwitchOffPWM( &pHandle->_Super );

  pHandle->PhaseAOffset /= (NB_CONVERSIONS/2);
  pHandle->PhaseBOffset /= (NB_CONVERSIONS/2);
  pHandle->PhaseCOffset /= (NB_CONVERSIONS/2);

  /* Change back function to be executed in ADCx_ISR */
  pHandle->_Super.pFctGetPhaseCurrents = &R3_2_GetPhaseCurrents;
  pHandle->_Super.pFctSetADCSampPointSectX = &R3_2_SetADCSampPointSectX;

  /* It over write TIMx CCRy wrongly written by FOC during Polarization so as to
     force 50% duty cycle on the three inverter legs */
  /* Disable TIMx preload */
  LL_TIM_OC_DisablePreload( TIMx, LL_TIM_CHANNEL_CH1 );
  LL_TIM_OC_DisablePreload( TIMx, LL_TIM_CHANNEL_CH2 );
  LL_TIM_OC_DisablePreload( TIMx, LL_TIM_CHANNEL_CH3 );

  LL_TIM_OC_SetCompareCH1(TIMx,pHandle->Half_PWMPeriod);
  LL_TIM_OC_SetCompareCH2(TIMx,pHandle->Half_PWMPeriod);
  LL_TIM_OC_SetCompareCH3(TIMx,pHandle->Half_PWMPeriod);

  LL_TIM_OC_EnablePreload( TIMx, LL_TIM_CHANNEL_CH1 );
  LL_TIM_OC_EnablePreload( TIMx, LL_TIM_CHANNEL_CH2 );
  LL_TIM_OC_EnablePreload( TIMx, LL_TIM_CHANNEL_CH3 );

  /* sector and phase sequence for the switch on phase */
  pHandle->_Super.Sector = SECTOR_4;

  /* It re-enable drive of TIMx CHy and CHyN by TIMx CHyRef*/
  LL_TIM_CC_EnableChannel(TIMx, TIMxCCER_MASK_CH123);
}

/**
 * @brief Computes the most recently converted motor phase currents
 *
 * @param  pHandle: handler of the current instance of the PWM component
 * 
 */
__weak void R3_2_GetPhaseCurrents( PWMC_Handle_t * pHdl, ab_t* pStator_Currents )
{
  PWMC_R3_2_Handle_t * pHandle = (PWMC_R3_2_Handle_t *) pHdl;
  
  TIM_TypeDef * TIMx = pHandle->pParams_str->TIMx;
  int32_t wAux;
  uint16_t hReg1;
  uint16_t hReg2;
  uint8_t bSector;

  /* disable ADC trigger source */
  LL_TIM_CC_DisableChannel(TIMx, LL_TIM_CHANNEL_CH4);

  bSector = pHandle->_Super.Sector;
  hReg1 = *pHandle->pParams_str->ADCDataReg1[bSector] * 2;
  hReg2 = *pHandle->pParams_str->ADCDataReg2[bSector] * 2;

  switch ( bSector )
  {
    case SECTOR_4:
    case SECTOR_5:
      /* Current on Phase C is not accessible     */
      /* Ia = PhaseAOffset - ADC converted value) */
      wAux = ( int32_t )( pHandle->PhaseAOffset ) - ( int32_t )( hReg1 );
      /* Saturation of Ia */
      if ( wAux < -INT16_MAX )
      {
        pStator_Currents->a = -INT16_MAX;
      }
      else  if ( wAux > INT16_MAX )
      {
        pStator_Currents->a = INT16_MAX;
      }
      else
      {
        pStator_Currents->a = ( int16_t )wAux;
      }

      /* Ib = PhaseBOffset - ADC converted value) */
        wAux = ( int32_t )( pHandle->PhaseBOffset ) - ( int32_t )( hReg2 );

      /* Saturation of Ib */
      if ( wAux < -INT16_MAX )
      {
        pStator_Currents->b = -INT16_MAX;
      }
      else  if ( wAux > INT16_MAX )
      {
        pStator_Currents->b = INT16_MAX;
      }
      else
      {
        pStator_Currents->b = ( int16_t )wAux;
      }
      break;

    case SECTOR_6:
    case SECTOR_1:
      /* Current on Phase A is not accessible     */
      /* Ib = PhaseBOffset - ADC converted value) */
      wAux = ( int32_t )( pHandle->PhaseBOffset ) - ( int32_t )( hReg1 );
      /* Saturation of Ib */
      if ( wAux < -INT16_MAX )
      {
        pStator_Currents->b = -INT16_MAX;
      }
      else  if ( wAux > INT16_MAX )
      {
        pStator_Currents->b = INT16_MAX;
      }
      else
      {
        pStator_Currents->b = ( int16_t )wAux;
      }

      /* Ic = PhaseCOffset - ADC converted value) */
      /* Ia = -Ic -Ib */
      wAux = ( int32_t )( pHandle->PhaseCOffset ) - ( int32_t )( hReg2 );
      wAux = -wAux - ( int32_t )pStator_Currents->b;

      /* Saturation of Ia */
      if ( wAux > INT16_MAX )
      {
        pStator_Currents->a = INT16_MAX;
      }
      else  if ( wAux < -INT16_MAX )
      {
        pStator_Currents->a = -INT16_MAX;
      }
      else
      {
        pStator_Currents->a = ( int16_t )wAux;
      }
      break;

    case SECTOR_2:
    case SECTOR_3:
      /* Current on Phase B is not accessible     */
      /* Ia = PhaseAOffset - ADC converted value) */
      wAux = ( int32_t )( pHandle->PhaseAOffset ) - ( int32_t )( hReg1 );
      /* Saturation of Ia */
      if ( wAux < -INT16_MAX )
      {
        pStator_Currents->a = -INT16_MAX;
      }
      else  if ( wAux > INT16_MAX )
      {
        pStator_Currents->a = INT16_MAX;
      }
      else
      {
        pStator_Currents->a = ( int16_t )wAux;
      }

      /* Ic = PhaseCOffset - ADC converted value) */
      /* Ib = -Ic -Ia */
      wAux = ( int32_t )( pHandle->PhaseCOffset ) - ( int32_t )( hReg2 );
      wAux = -wAux -  ( int32_t )pStator_Currents->a;

      /* Saturation of Ib */
      if ( wAux > INT16_MAX )
      {
        pStator_Currents->b = INT16_MAX;
      }
      else  if ( wAux < -INT16_MAX )
      {
        pStator_Currents->b = -INT16_MAX;
      }
      else
      {
        pStator_Currents->b = ( int16_t )wAux;
      }
      break;

    default:
      break;
  }


  pHandle->_Super.Ia = pStator_Currents->a;
  pHandle->_Super.Ib = pStator_Currents->b;
  pHandle->_Super.Ic = -pStator_Currents->a - pStator_Currents->b;

  if(pHandle->_Super.OverCurrent && ((abs(pHandle->_Super.Ia) > pHandle->_Super.OverCurrent) || (abs(pHandle->_Super.Ia) > pHandle->_Super.OverCurrent) || (abs(pHandle->_Super.Ic) > pHandle->_Super.OverCurrent))){
	  pHandle->_Super.OverCurrentCyclesCounter++;
	  if(pHandle->_Super.OverCurrentCyclesCounter > pHandle->_Super.OverCurrentCycles){
		  pHandle->OverCurrentFlag = true;
	  	  R3_2_SwitchOffPWM(pHdl);
	  }
  }else{
	  pHandle->_Super.OverCurrentCyclesCounter = 0;
  }
}

/**
  * @brief  Implementation of PWMC_GetPhaseCurrents to be performed during
  *         Polarization. It sum up injected conversion data into PhaseAOffset and
  *         PhaseBOffset to compute the offset introduced in the current feedback
  *         network. It is required to proper configure ADC inputs before to enable
  *         the offset computation.
  * @param  pHandle: handler of the current instance of the PWM component
  * @retval It always returns {0,0} in ab_t format
  */
void R3_2_HFCurrentsPolarizationAB( PWMC_Handle_t * pHdl, ab_t * pStator_Currents )
{
  PWMC_R3_2_Handle_t * pHandle = (PWMC_R3_2_Handle_t *) pHdl;
  TIM_TypeDef * TIMx = pHandle->pParams_str->TIMx;

  /* disable ADC trigger source */
  LL_TIM_CC_DisableChannel(TIMx, LL_TIM_CHANNEL_CH4);

  if ( pHandle->PolarizationCounter < NB_CONVERSIONS )
  {
    pHandle->PhaseAOffset += *pHandle->pParams_str->ADCDataReg1[pHandle->PolarizationSector];
    pHandle->PhaseBOffset += *pHandle->pParams_str->ADCDataReg2[pHandle->PolarizationSector];
    pHandle->PolarizationCounter++;
  }

  /* during offset Polarization no current is flowing in the phases */
  pStator_Currents->a = 0;
  pStator_Currents->b = 0;
}

/**
  * @brief  Implementation of PWMC_GetPhaseCurrents to be performed during
  *         Polarization. It sum up injected conversion data into PhaseCOffset
  *         to compute the offset introduced in the current feedback
  *         network. It is required to proper configure ADC input before to enable
  *         the offset computation.
  * @param  pHandle: handler of the current instance of the PWM component
  * @retval It always returns {0,0} in ab_t format
  */
void R3_2_HFCurrentsPolarizationC( PWMC_Handle_t * pHdl, ab_t * pStator_Currents )
{
  PWMC_R3_2_Handle_t * pHandle = (PWMC_R3_2_Handle_t *) pHdl;
  TIM_TypeDef * TIMx = pHandle->pParams_str->TIMx;  

  /* disable ADC trigger source */
  LL_TIM_CC_DisableChannel(TIMx, LL_TIM_CHANNEL_CH4);

  if ( pHandle->PolarizationCounter < NB_CONVERSIONS )
  {
    pHandle->PhaseCOffset += *pHandle->pParams_str->ADCDataReg2[pHandle->PolarizationSector];
    pHandle->PolarizationCounter++;
  }

  /* during offset Polarization no current is flowing in the phases */
  pStator_Currents->a = 0;
  pStator_Currents->b = 0;
}

/**
  * @brief  It turns on low sides switches. This function is intended to be
  *         used for charging boot capacitors of driving section. It has to be
  *         called each motor start-up when using high voltage drivers
  * @param  pHandle: handler of the current instance of the PWM component
  * @retval none
  */
__weak void R3_2_TurnOnLowSides( PWMC_Handle_t * pHdl )
{
  PWMC_R3_2_Handle_t * pHandle = (PWMC_R3_2_Handle_t *) pHdl;
  TIM_TypeDef* TIMx = pHandle->pParams_str->TIMx;

  pHandle->_Super.TurnOnLowSidesAction = true;

  /* Clear Update Flag */
  LL_TIM_ClearFlag_UPDATE(TIMx);

  /*Turn on the three low side switches */
  LL_TIM_OC_SetCompareCH1(TIMx,0);
  LL_TIM_OC_SetCompareCH2(TIMx,0);
  LL_TIM_OC_SetCompareCH3(TIMx,0);

  /* Wait until next update */
  while (LL_TIM_IsActiveFlag_UPDATE(TIMx) == RESET)
  {}
  LL_TIM_ClearFlag_UPDATE( TIMx );

  /* Main PWM Output Enable */
  LL_TIM_EnableAllOutputs(TIMx);
  if ( (pHandle->pParams_str->LowSideOutputs) == ES_GPIO )
  {
    LL_GPIO_SetOutputPin (pHandle->pParams_str->pwm_en_u_port, pHandle->pParams_str->pwm_en_u_pin);
    LL_GPIO_SetOutputPin (pHandle->pParams_str->pwm_en_v_port, pHandle->pParams_str->pwm_en_v_pin);
    LL_GPIO_SetOutputPin (pHandle->pParams_str->pwm_en_w_port, pHandle->pParams_str->pwm_en_w_pin);
  }
  return;
}

/**
  * @brief  It enables PWM generation on the proper Timer peripheral acting on MOE
  *         bit
  * @param  pHandle: handler of the current instance of the PWM component
  * @retval none
  */
__weak void R3_2_SwitchOnPWM( PWMC_Handle_t * pHdl )
{  

  PWMC_R3_2_Handle_t * pHandle = (PWMC_R3_2_Handle_t *) pHdl;
  TIM_TypeDef* TIMx = pHandle->pParams_str->TIMx;
  pHdl->PWM_off = false;

  pHandle->_Super.TurnOnLowSidesAction = false;

  /* Set all duty to 50% */
  LL_TIM_OC_SetCompareCH1(TIMx, (uint32_t)(pHandle->Half_PWMPeriod  >> 1));
  LL_TIM_OC_SetCompareCH2(TIMx, (uint32_t)(pHandle->Half_PWMPeriod  >> 1));
  LL_TIM_OC_SetCompareCH3(TIMx, (uint32_t)(pHandle->Half_PWMPeriod  >> 1));
  LL_TIM_OC_SetCompareCH4(TIMx, (uint32_t)(pHandle->Half_PWMPeriod - 5u));

  /* wait for a new PWM period */
  LL_TIM_ClearFlag_UPDATE(TIMx);
  while ( LL_TIM_IsActiveFlag_UPDATE( TIMx ) == 0 )
  {}
  /* Clear Update Flag */
  LL_TIM_ClearFlag_UPDATE(TIMx);

  /* Main PWM Output Enable */
  TIMx->BDTR |= LL_TIM_OSSI_ENABLE;
  LL_TIM_EnableAllOutputs( TIMx );

  if ( ( pHandle->pParams_str->LowSideOutputs ) == ES_GPIO )
  {
    if ( LL_TIM_CC_IsEnabledChannel(TIMx,TIMxCCER_MASK_CH123) != 0u )
    {
      LL_GPIO_SetOutputPin( pHandle->pParams_str->pwm_en_u_port, pHandle->pParams_str->pwm_en_u_pin );
      LL_GPIO_SetOutputPin( pHandle->pParams_str->pwm_en_v_port, pHandle->pParams_str->pwm_en_v_pin );
      LL_GPIO_SetOutputPin( pHandle->pParams_str->pwm_en_w_port, pHandle->pParams_str->pwm_en_w_pin );
    }
    else
    {
      /* It is executed during Polarization phase the EN signal shall stay off */
      LL_GPIO_ResetOutputPin( pHandle->pParams_str->pwm_en_u_port, pHandle->pParams_str->pwm_en_u_pin );
      LL_GPIO_ResetOutputPin( pHandle->pParams_str->pwm_en_v_port, pHandle->pParams_str->pwm_en_v_pin );
      LL_GPIO_ResetOutputPin( pHandle->pParams_str->pwm_en_w_port, pHandle->pParams_str->pwm_en_w_pin );
    }
  }

  /* Clear Update Flag */
  LL_TIM_ClearFlag_UPDATE( TIMx );
  /* Enable Update IRQ */
  LL_TIM_EnableIT_UPDATE(TIMx);

  return;
}

/**
  * @brief  It disables PWM generation on the proper Timer peripheral acting on
  *         MOE bit
  * @param  pHandle: handler of the current instance of the PWM component
  * @retval none
  */
__weak void R3_2_SwitchOffPWM( PWMC_Handle_t * pHdl )
{ 
  PWMC_R3_2_Handle_t * pHandle = (PWMC_R3_2_Handle_t *) pHdl;
  TIM_TypeDef* TIMx = pHandle->pParams_str->TIMx;
  pHdl->PWM_off = true;

  /* Disable UPDATE ISR */
  LL_TIM_DisableIT_UPDATE( TIMx );
  
  pHandle->_Super.TurnOnLowSidesAction = false;

  /* Main PWM Output Disable */
  LL_TIM_DisableAllOutputs( TIMx );
  if ( (pHandle->pParams_str->LowSideOutputs) == ES_GPIO )
  {
    LL_GPIO_ResetOutputPin (pHandle->pParams_str->pwm_en_u_port, pHandle->pParams_str->pwm_en_u_pin);
    LL_GPIO_ResetOutputPin (pHandle->pParams_str->pwm_en_v_port, pHandle->pParams_str->pwm_en_v_pin);
    LL_GPIO_ResetOutputPin (pHandle->pParams_str->pwm_en_w_port, pHandle->pParams_str->pwm_en_w_pin);
  }
  
  /* wait for a new PWM period */
  LL_TIM_ClearFlag_UPDATE(TIMx);
  while ( LL_TIM_IsActiveFlag_UPDATE( TIMx ) == 0 )
  {}
  LL_TIM_ClearFlag_UPDATE(TIMx);

  return;
}

/**
  * @brief Writes into peripheral registers the new duty cycles and
  *        sampling point.
  * @param  pHandle: handler of the current instance of the PWM component
  * @param hCCR4Reg: new capture/compare register value.
  * @retval Error status
  */
uint16_t R3_2_WriteTIMRegisters( PWMC_Handle_t * pHdl, uint16_t hCCR4Reg )
{
  PWMC_R3_2_Handle_t * pHandle = (PWMC_R3_2_Handle_t *) pHdl;
  TIM_TypeDef * TIMx = pHandle->pParams_str->TIMx;
  uint16_t hAux;

  LL_TIM_OC_SetCompareCH1( TIMx, pHandle->_Super.CntPhA );
  LL_TIM_OC_SetCompareCH2( TIMx, pHandle->_Super.CntPhB );
  LL_TIM_OC_SetCompareCH3( TIMx, pHandle->_Super.CntPhC );
  LL_TIM_OC_SetCompareCH4( TIMx, hCCR4Reg );

  /* Limit for update event */
  /* Check the status of SOFOC flag. If it is set, an update event has occurred 
     and thus the FOC rate is too high */
  if ( LL_TIM_CC_IsEnabledChannel(TIMx, LL_TIM_CHANNEL_CH4))
  {
    hAux = MC_FOC_DURATION;
  }
  else
  {
    hAux = MC_NO_ERROR;
  }
  if ( pHandle->_Super.SWerror == 1u )
  {
    hAux = MC_FOC_DURATION;
    pHandle->_Super.SWerror = 0u;
  }
  return hAux;
}

/**
 * @brief  Configure the ADC for the current sampling during Polarization.
 *         It means set the sampling point via TIMx_Ch4 value and polarity
 *         ADC sequence length and channels.
 *         And call the WriteTIMRegisters method.
 * @param pHdl: handler of the current instance of the PWM component
 * @retval none
 */
uint16_t R3_2_SetADCSampPointPolarization( PWMC_Handle_t * pHdl)
{
  PWMC_R3_2_Handle_t * pHandle = ( PWMC_R3_2_Handle_t * )pHdl;

  pHandle->_Super.Sector = pHandle->PolarizationSector;

  return R3_2_WriteTIMRegisters( &pHandle->_Super, (uint32_t)(pHandle->Half_PWMPeriod - 1u) );
}

/**
  * @brief  Configure the ADC for the current sampling related to sector 1.
  *         It means set the sampling point via TIMx_Ch4 value and polarity
  *         ADC sequence length and channels.
  *         And call the WriteTIMRegisters method.
  * @param  pHandle: handler of the current instance of the PWM component
  * @retval none
  */
__weak uint16_t R3_2_SetADCSampPointSectX( PWMC_Handle_t * pHdl )
{
  PWMC_R3_2_Handle_t * pHandle = ( PWMC_R3_2_Handle_t * )pHdl;

  /* Set CC4 as PWM mode 2 (default) */
  pHandle->PWM_Mode = LL_TIM_OCMODE_PWM2;
  uint16_t hCntSmp;
  uint16_t hDeltaDuty;
  register uint16_t lowDuty = pHdl->lowDuty;
  register uint16_t midDuty = pHdl->midDuty;

  /* Check if sampling AB in the middle of PWM is possible */
  if ( ( uint16_t )( pHandle->Half_PWMPeriod - lowDuty ) > pHandle->pParams_str->Tafter )
  {
    /* When it is possible to sample in the middle of the PWM period, always sample the same phases
     * (AB are chosen) for all sectors in order to not induce current discontinuities when there are differences
     * between offsets */

    /* sector number needed by GetPhaseCurrent, phase A and B are sampled wIch corresponds
     * to sector 4 */
    pHandle->_Super.Sector = SECTOR_4;

    /* set sampling  point trigger in the middle of PWM period */
    hCntSmp = ( uint32_t )( pHandle->Half_PWMPeriod ) - 1u;
  }
  else
  {
    /* ADC Injected sequence configuration. The stator phase with minimum value of complementary
    duty cycle is set as first. In every sector there is always one phase with maximum complementary duty,
    one with minimum complementary duty and one with variable complementary duty. In this case, phases
    with variable complementary duty and with maximum duty are converted and the first will be always
    the phase with variable complementary duty cycle */

    /* Crossing Point Searching */
    hDeltaDuty = ( uint16_t )( lowDuty - midDuty );

    /* Definition of crossing point */
    if ( hDeltaDuty > ( uint16_t )( pHandle->Half_PWMPeriod - lowDuty ) * 2u )
    {
      /* hTbefore = 2*Ts + Tc, where Ts = Sampling time of ADC, Tc = Conversion Time of ADC */
      hCntSmp = lowDuty - pHandle->pParams_str->Tbefore;
    }
    else
    {
      /* hTafter = DT + max(Trise, Tnoise) */
      hCntSmp = lowDuty + pHandle->pParams_str->Tafter;

      if ( hCntSmp >= pHandle->Half_PWMPeriod )
      {
        /* It must be changed the trigger direction from positive to negative
             to sample after middle of PWM*/
        /* Set CC4 as PWM mode 1 */
        pHandle->PWM_Mode = LL_TIM_OCMODE_PWM1;
        hCntSmp = ( 2u * pHandle->Half_PWMPeriod ) - hCntSmp - 1u;
      }
    }
  }

  return R3_2_WriteTIMRegisters( &pHandle->_Super, hCntSmp );
}

/**
  * @brief  It contains the TIMx Update event interrupt
  * @param  pHandle: handler of the current instance of the PWM component
  * @retval none
  */
__weak void * R3_2_TIMx_UP_IRQHandler( PWMC_R3_2_Handle_t * pHandle)
{
  TIM_TypeDef* TIMx = pHandle->pParams_str->TIMx;
  ADC_TypeDef * ADCx_1 = pHandle->pParams_str->ADCx_1;
  ADC_TypeDef * ADCx_2 = pHandle->pParams_str->ADCx_2;

  /* Disabling trigger to avoid unwanted conversion */
  LL_ADC_INJ_StopConversionExtTrig(ADCx_1);
  LL_ADC_INJ_StopConversionExtTrig(ADCx_2);

  /* Set next current channel according to sector  */
  ADCx_1->JSQR = pHandle->pParams_str->ADCConfig1[pHandle->_Super.Sector];
  ADCx_2->JSQR = pHandle->pParams_str->ADCConfig2[pHandle->_Super.Sector];

  /* Enabling next Trigger */
  LL_TIM_CC_EnableChannel(TIMx, LL_TIM_CHANNEL_CH4);

  LL_ADC_INJ_SetTriggerSource(ADCx_1, pHandle->ADC_ExternalTriggerInjected);
  LL_ADC_INJ_SetTriggerSource(ADCx_2, pHandle->ADC_ExternalTriggerInjected);

  LL_ADC_INJ_StartConversionExtTrig(ADCx_1, LL_ADC_INJ_TRIG_EXT_RISING);
  LL_ADC_INJ_StartConversionExtTrig(ADCx_2, LL_ADC_INJ_TRIG_EXT_RISING);
  
  /* Set edge detection trigger according to PWM Mode 1 or 2 */
  LL_TIM_OC_SetMode(TIMx, LL_TIM_CHANNEL_CH4, pHandle->PWM_Mode);

  return &( pHandle->_Super.Motor );
}

/**
 * @brief  It contains the Break event interrupt
 * @param  pHandle: handler of the current instance of the PWM component
 * @retval none
 */
__weak void *R3_2_BRK_IRQHandler(PWMC_R3_2_Handle_t *pHandle)
{

  if ((pHandle->pParams_str->LowSideOutputs)== ES_GPIO)
  {
     LL_GPIO_ResetOutputPin(pHandle->pParams_str->pwm_en_u_port, pHandle->pParams_str->pwm_en_u_pin);
     LL_GPIO_ResetOutputPin(pHandle->pParams_str->pwm_en_v_port, pHandle->pParams_str->pwm_en_v_pin);
     LL_GPIO_ResetOutputPin(pHandle->pParams_str->pwm_en_w_port, pHandle->pParams_str->pwm_en_w_pin);
  }
  pHandle->OverCurrentFlag = true;

  return &(pHandle->_Super.Motor);
}

/**
  * @brief  It is used to check if an over current occurred since last call.
  * @param  pHandle: handler of the current instance of the PWM component
  * @retval uint16_t It returns MC_BREAK_IN whether an over current has been
  *                  detected since last method call, MC_NO_FAULTS otherwise.
  */
__weak uint16_t R3_2_IsOverCurrentOccurred( PWMC_Handle_t * pHdl )
{
  PWMC_R3_2_Handle_t * pHandle = (PWMC_R3_2_Handle_t *) pHdl;
  uint16_t retVal = MC_NO_FAULTS;
  if (pHandle->OverCurrentFlag == true )
  {
    retVal = MC_BREAK_IN;
    pHandle->OverCurrentFlag = false;
  }
  return retVal;
}

/**
* @}
*/

/**
* @}
*/

/** @} */

/******************* (C) COPYRIGHT 2019 STMicroelectronics *****END OF FILE****/
